TinyCircuits/TinyCircuits-Whisker-Light-Sensor-AST1012/images/AST1012-Product-Photo-01.png

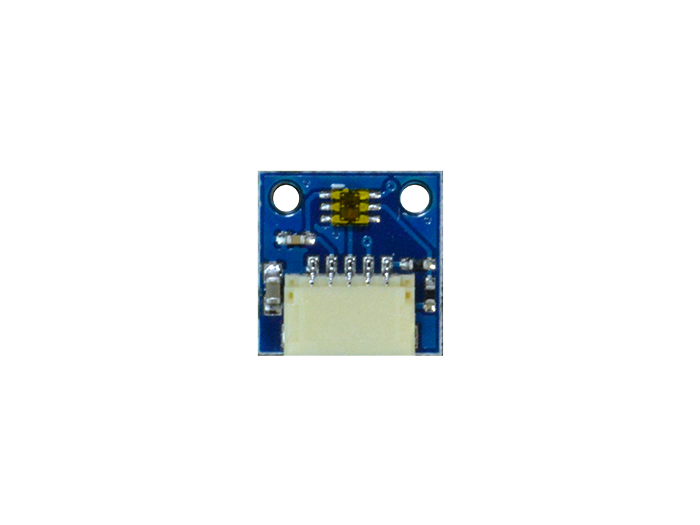
images/AST1012-Product-Photo-01.png
