TinyCircuits/TinyCircuits-Whisker-Light-Sensor-AST1012/images/AST1012-Tutorial-Image-03.png

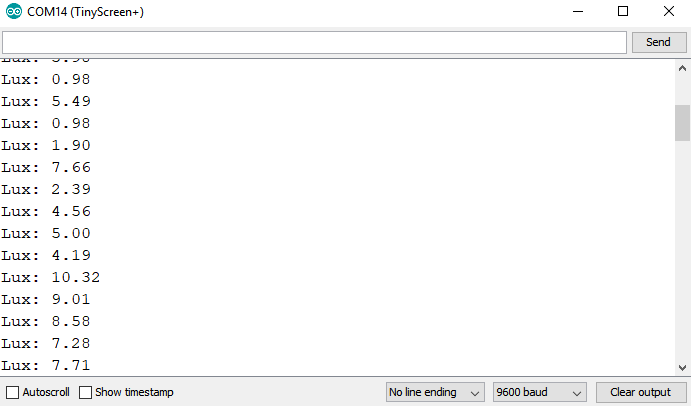
images/AST1012-Tutorial-Image-03.png
